jdekozak/Tranxen200/UnitTests/FakeMidiSettingIO.h

#pragma once

#include <iostream>

namespace THCRecords
{
namespace Device
{

struct FakeMidiSettingIO
{
  int up = 0;
  int down = 0;
  int next = 0;
  void setup()
  {
    std::cout << "FakeMidiSetting::setup" << std::endl;
  }
  int getUp() const
  {
    std::cout << "FakeMidiSetting::getUp::" << up << std::endl;
    return up;
  }
  int getDown() const
  {
    std::cout << "FakeMidiSetting::getDown::" << down << std::endl;
    return down;
  }
  int getNext() const
  {
    std::cout << "FakeMidiSetting::getNext::" << next << std::endl;
    return next;
  }
};

typedef FakeMidiSettingIO TheMidiSetting;
TheMidiSetting midiDevice;

}
}
